edrobotics/rescue_maze_2024/vision/log/sorted/H/4cam2190.png

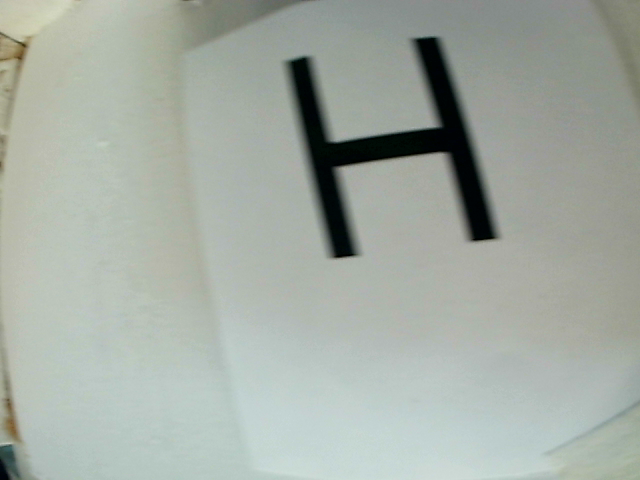
vision/log/sorted/H/4cam2190.png
