edrobotics/rescue_maze_2024/vision/log/sorted/H/5cam2187.png

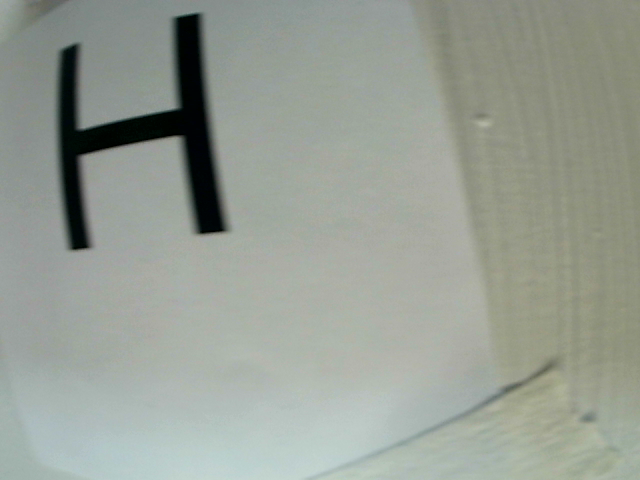
vision/log/sorted/H/5cam2187.png
