edrobotics/rescue_maze_2024/vision/log/sorted/H/6cam2188.png

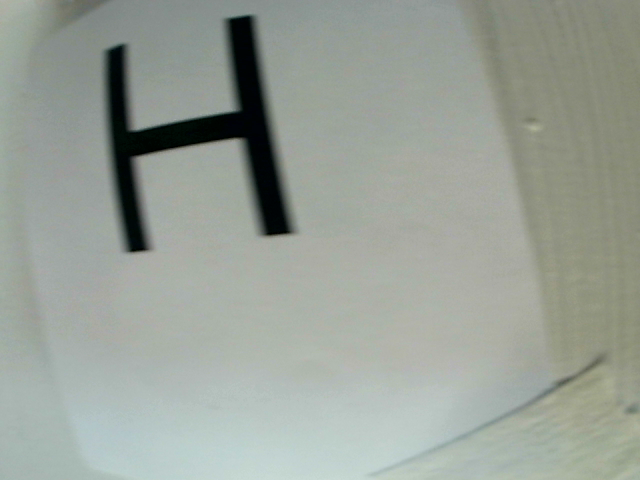
vision/log/sorted/H/6cam2188.png
