edrobotics/rescue_maze_2024/vision/log/sorted/H/7cam2189.png

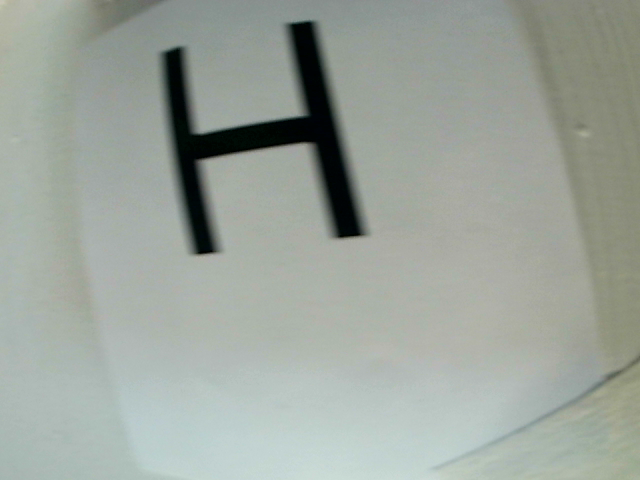
vision/log/sorted/H/7cam2189.png
