edrobotics/rescue_maze_2024/vision/log/sorted/H/8cam2171.png

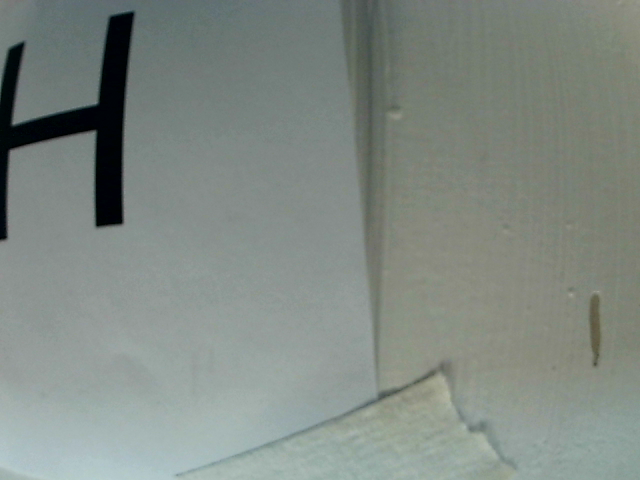
vision/log/sorted/H/8cam2171.png
