edrobotics/rescue_maze_2024/vision/log/sorted/red/17cam2191.png

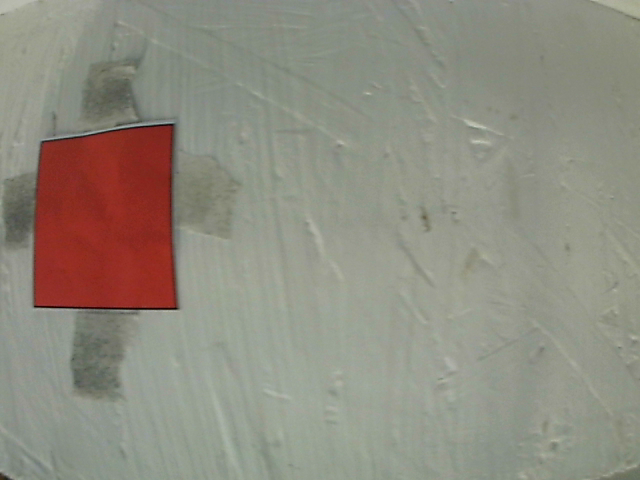
vision/log/sorted/red/17cam2191.png
