edrobotics/rescue_maze_2024/vision/log/sorted/red/18cam2193.png

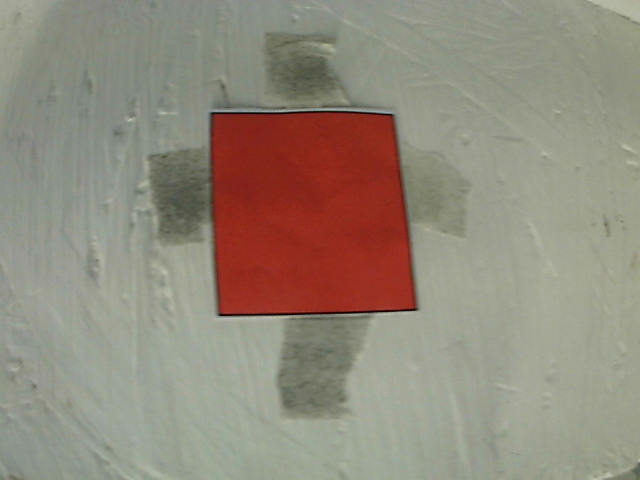
vision/log/sorted/red/18cam2193.png
