edrobotics/rescue_maze_2024/vision/log/sorted/red/19cam2192.png

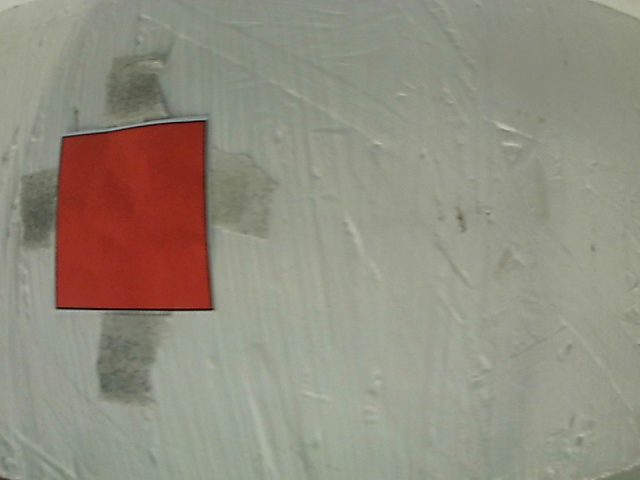
vision/log/sorted/red/19cam2192.png
