edrobotics/rescue_maze_2024/vision/log/sorted/red/20cam2194.png

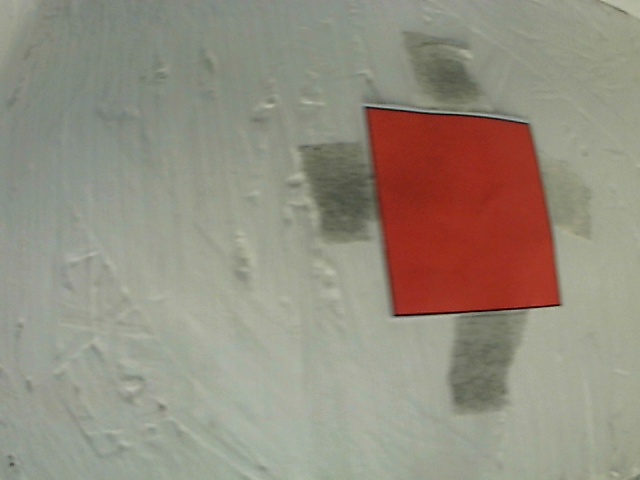
vision/log/sorted/red/20cam2194.png
