edrobotics/rescue_maze_2024/vision/log/sorted/red/21cam1767.png

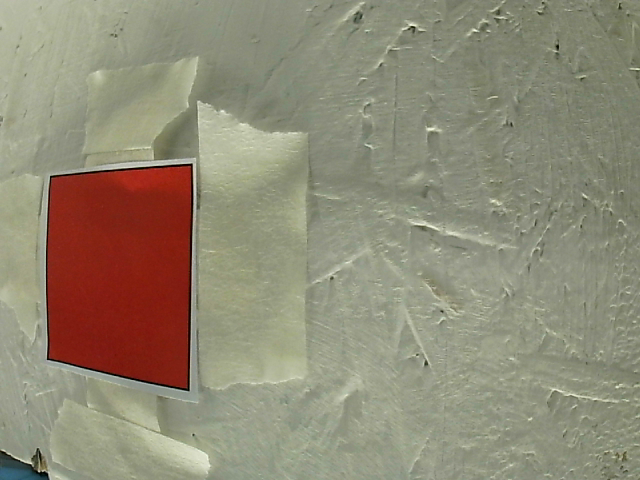
vision/log/sorted/red/21cam1767.png
