edrobotics/rescue_maze_2024/vision/log/sorted/red/24cam1758.png

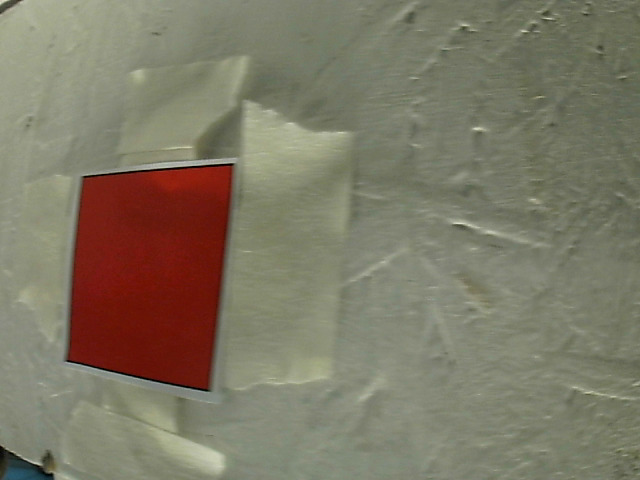
vision/log/sorted/red/24cam1758.png
