edrobotics/rescue_maze_2024/vision/log/sorted/red/31cam1776.png

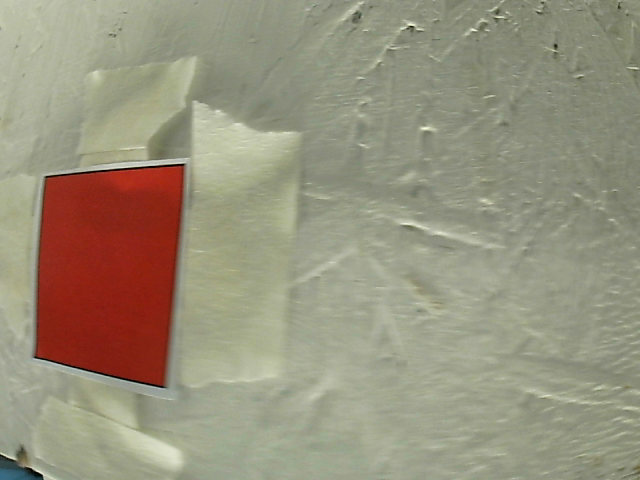
vision/log/sorted/red/31cam1776.png
