edrobotics/rescue_maze_2024/vision/log/sorted/red/34cam1777.png

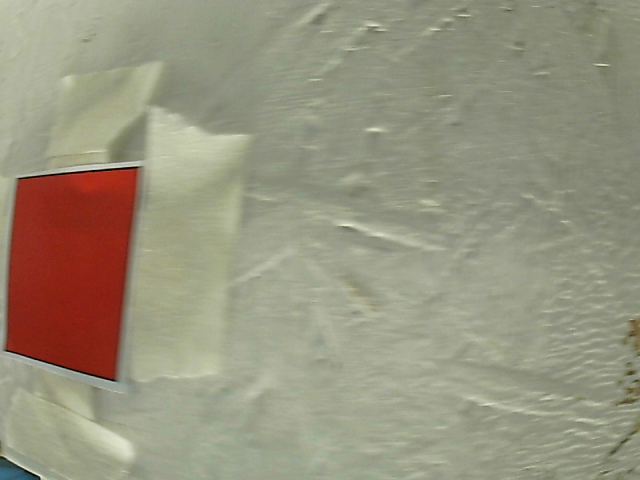
vision/log/sorted/red/34cam1777.png
