edrobotics/rescue_maze_2024/vision/log/sorted/red/cam284.png

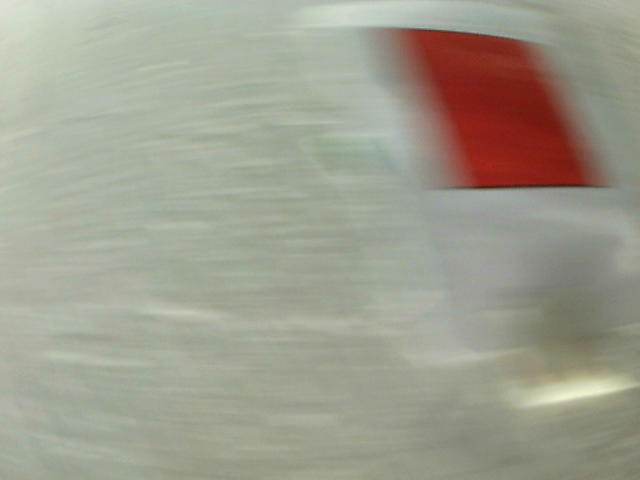
vision/log/sorted/red/cam284.png
