edrobotics/rescue_maze_2024/vision/log/sorted/red/cam1135.png

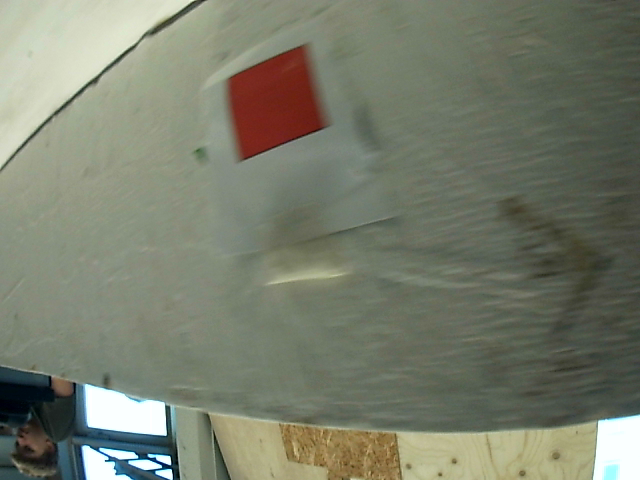
vision/log/sorted/red/cam1135.png
