edrobotics/rescue_maze_2024/vision/log/sorted/red/cam1257.png

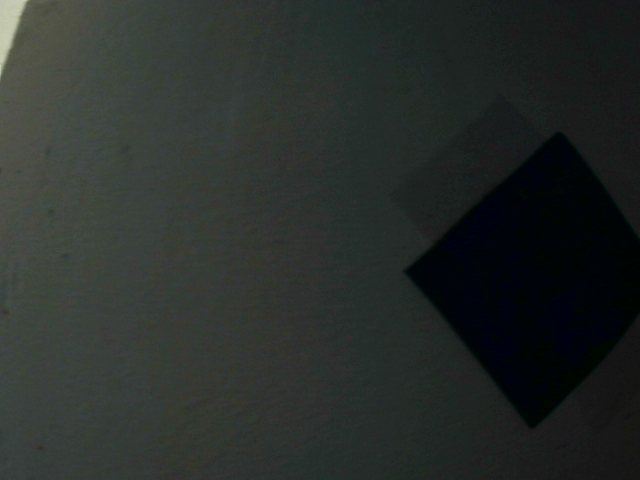
vision/log/sorted/red/cam1257.png
