edrobotics/rescue_maze_2024/vision/log/sorted/red/cam2422.png

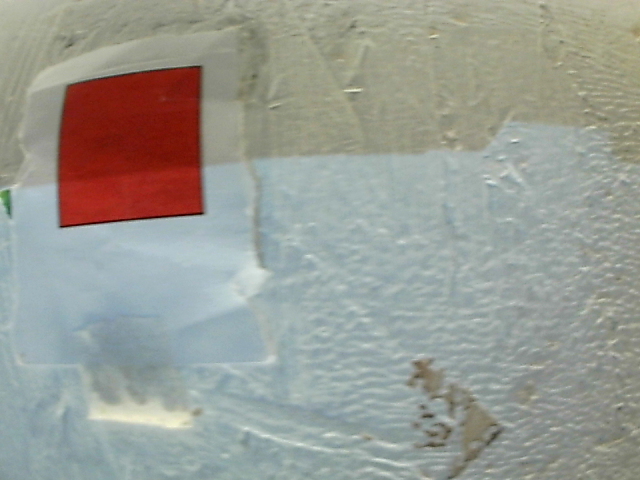
vision/log/sorted/red/cam2422.png
