edrobotics/rescue_maze_2024/vision/log/sorted/red/cam2428.png

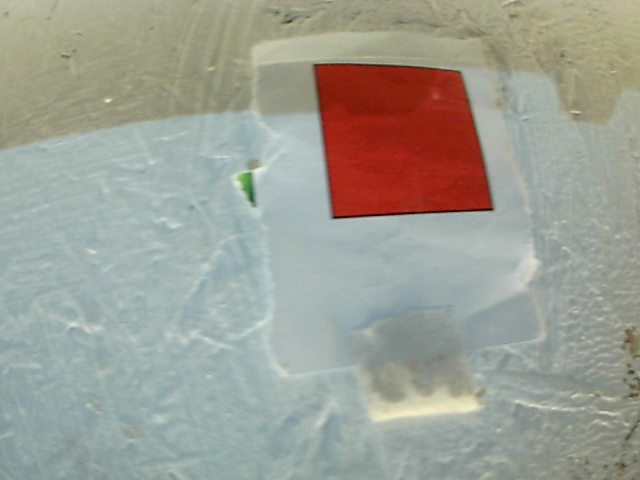
vision/log/sorted/red/cam2428.png
