edrobotics/rescue_maze_2024/vision/log/sorted/red/cam2500.png

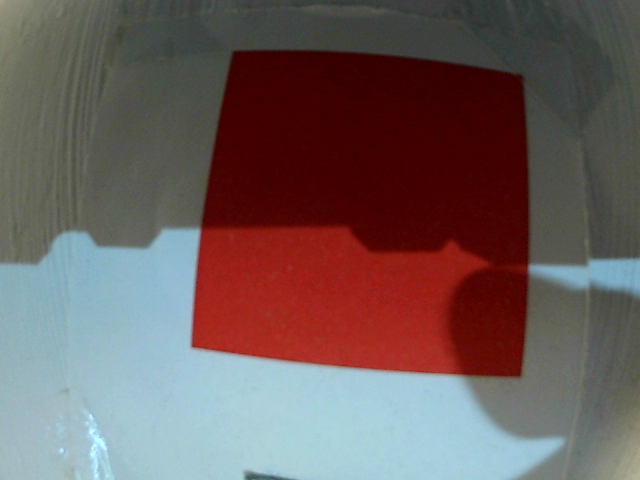
vision/log/sorted/red/cam2500.png
