edrobotics/rescue_maze_2024/vision/log/sorted/yellow/17cam2204.png

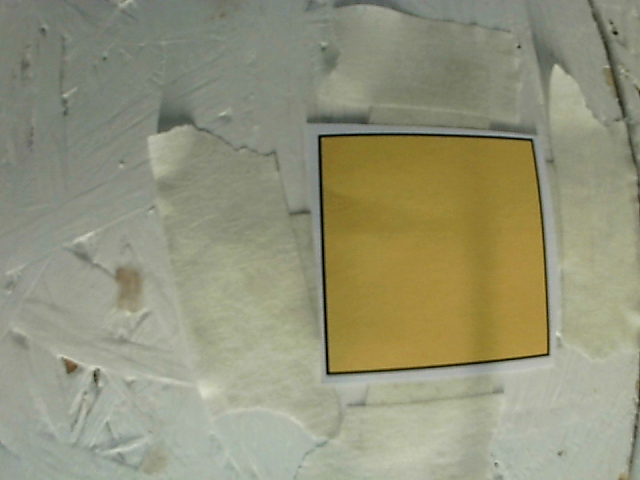
vision/log/sorted/yellow/17cam2204.png
