edrobotics/rescue_maze_2024/vision/log/sorted/yellow/18cam2202.png

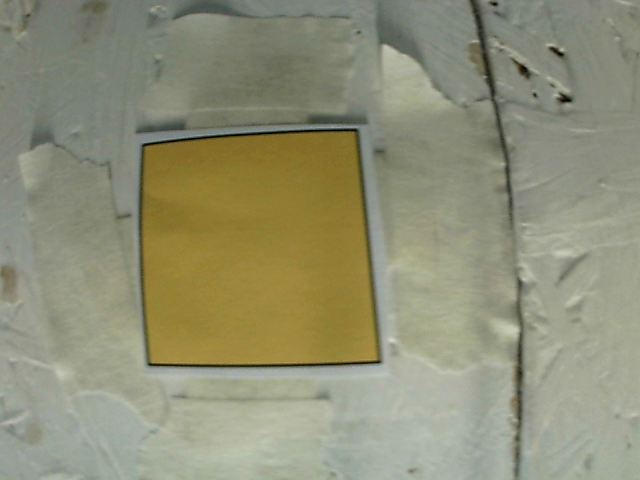
vision/log/sorted/yellow/18cam2202.png
