edrobotics/rescue_maze_2024/vision/log/sorted/yellow/19cam2203.png

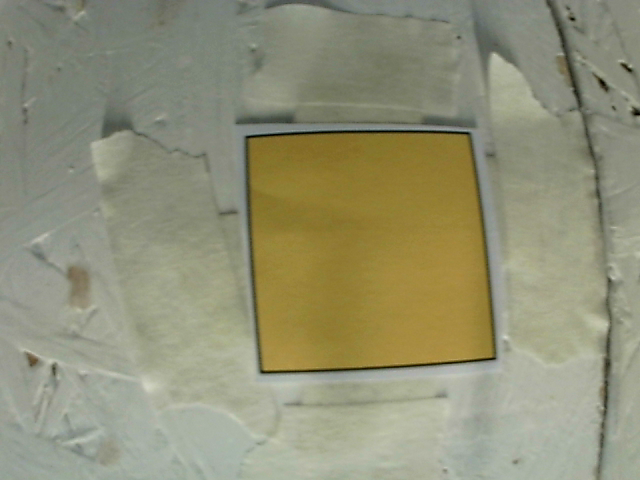
vision/log/sorted/yellow/19cam2203.png
