edrobotics/rescue_maze_2024/vision/log/sorted/yellow/20cam2108.png

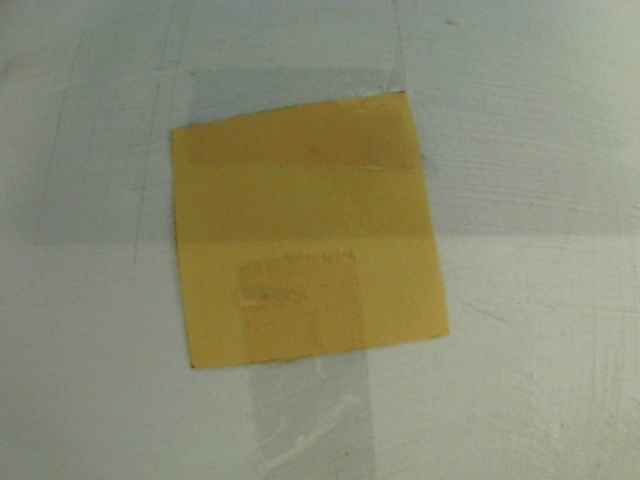
vision/log/sorted/yellow/20cam2108.png
