edrobotics/rescue_maze_2024/vision/log/sorted/yellow/21cam2105.png

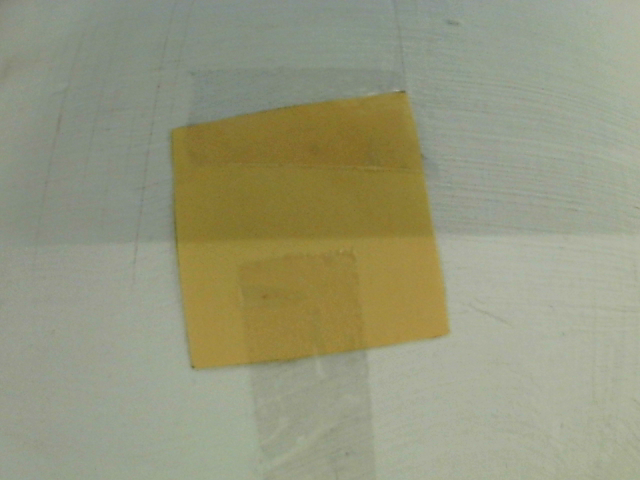
vision/log/sorted/yellow/21cam2105.png
