edrobotics/rescue_maze_2024/vision/log/sorted/yellow/22cam2104.png

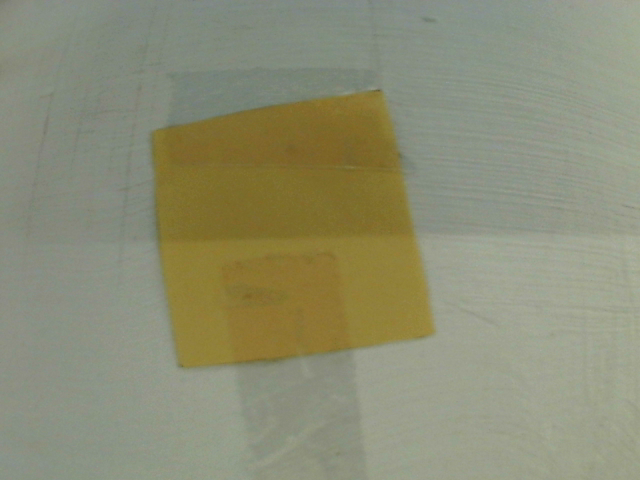
vision/log/sorted/yellow/22cam2104.png
