edrobotics/rescue_maze_2024/vision/log/sorted/yellow/23cam2110.png

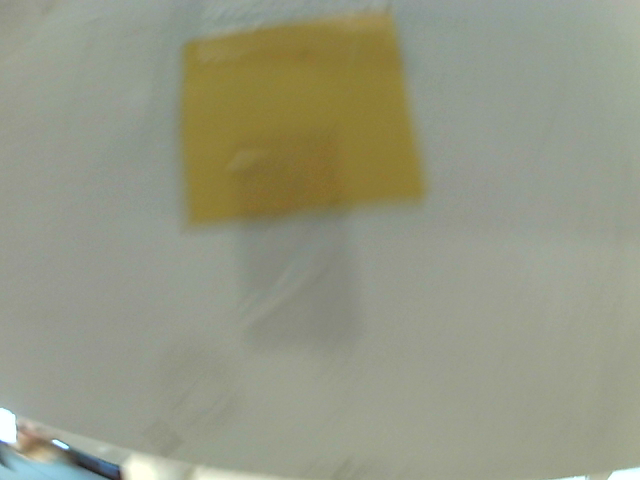
vision/log/sorted/yellow/23cam2110.png
