edrobotics/rescue_maze_2024/vision/log/sorted/yellow/25cam2107.png

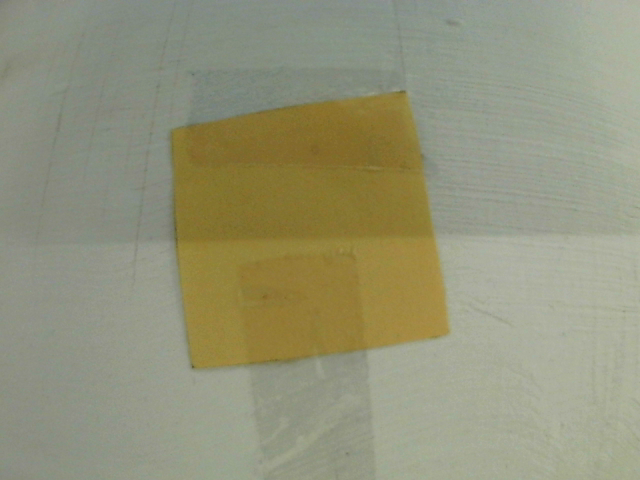
vision/log/sorted/yellow/25cam2107.png
