edrobotics/rescue_maze_2024/vision/log/sorted/yellow/26cam2103.png

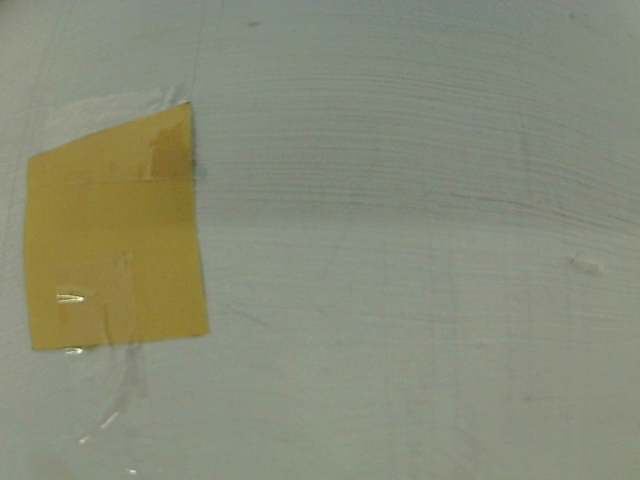
vision/log/sorted/yellow/26cam2103.png
