edrobotics/rescue_maze_2024/vision/log/sorted/yellow/cam290.png

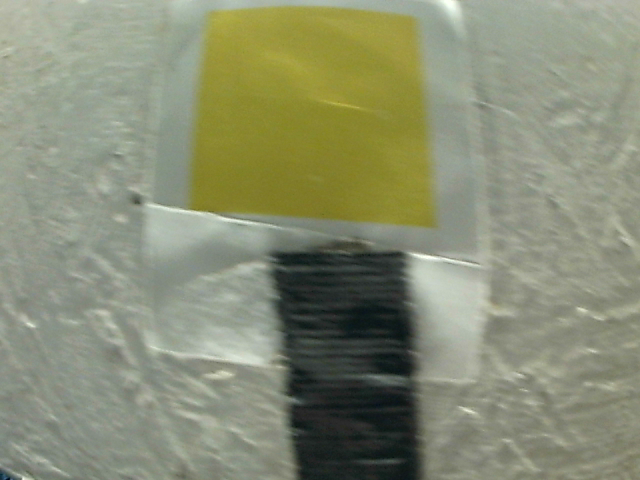
vision/log/sorted/yellow/cam290.png
