edrobotics/rescue_maze_2024/vision/log/sorted/yellow/cam292.png

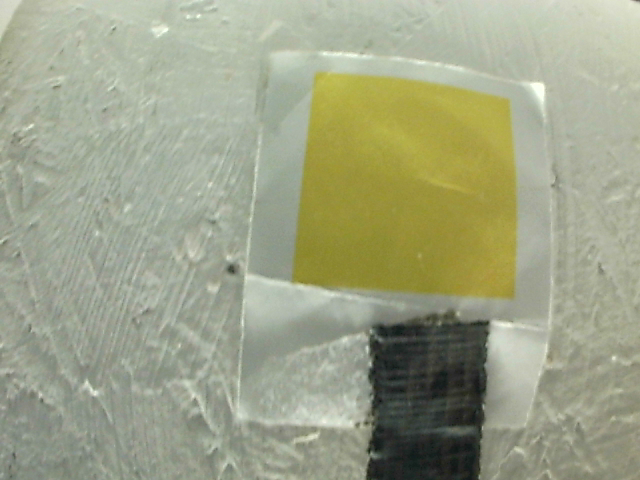
vision/log/sorted/yellow/cam292.png
