edrobotics/rescue_maze_2024/vision/log/sorted/yellow/cam294.png

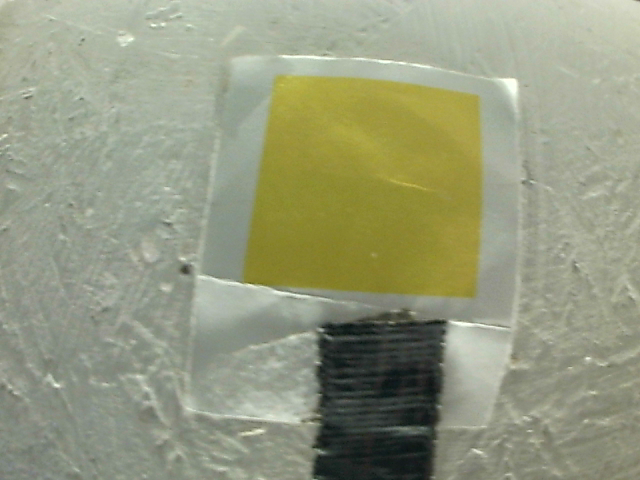
vision/log/sorted/yellow/cam294.png
