edrobotics/rescue_maze_2024/vision/log/sorted/yellow/cam296.png

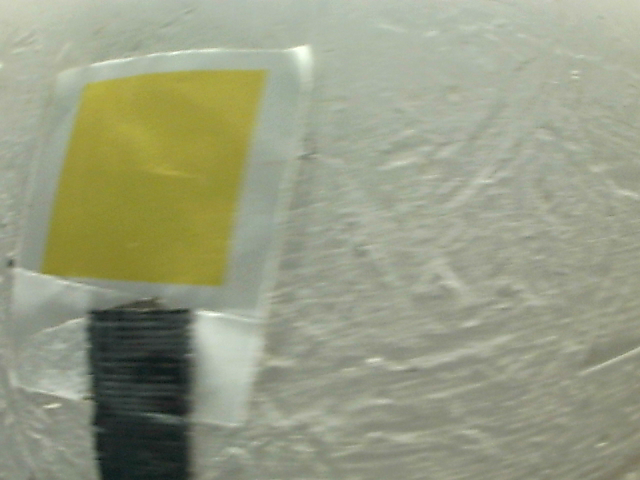
vision/log/sorted/yellow/cam296.png
