edrobotics/rescue_maze_2024/vision/log/sorted/yellow/cam1139.png

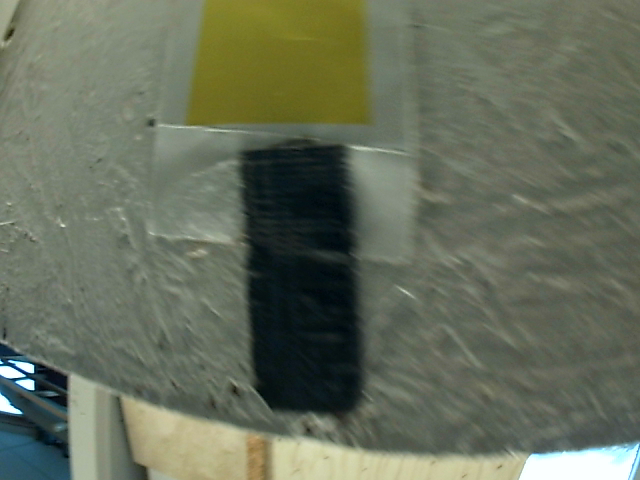
vision/log/sorted/yellow/cam1139.png
