edrobotics/rescue_maze_2024/vision/log/sorted/yellow/cam1141.png

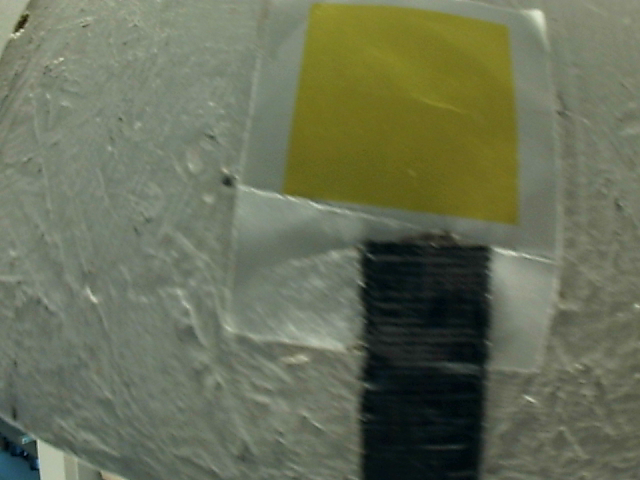
vision/log/sorted/yellow/cam1141.png
