edrobotics/rescue_maze_2024/vision/log/sorted/yellow/cam1145.png

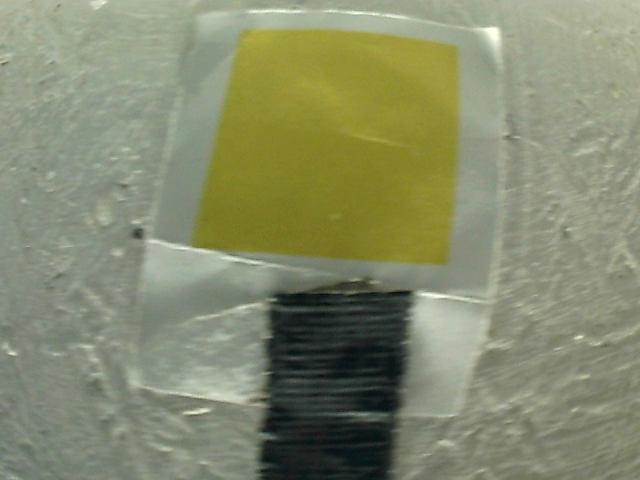
vision/log/sorted/yellow/cam1145.png
