edrobotics/rescue_maze_2024/vision/log/sorted/yellow/cam2214.png

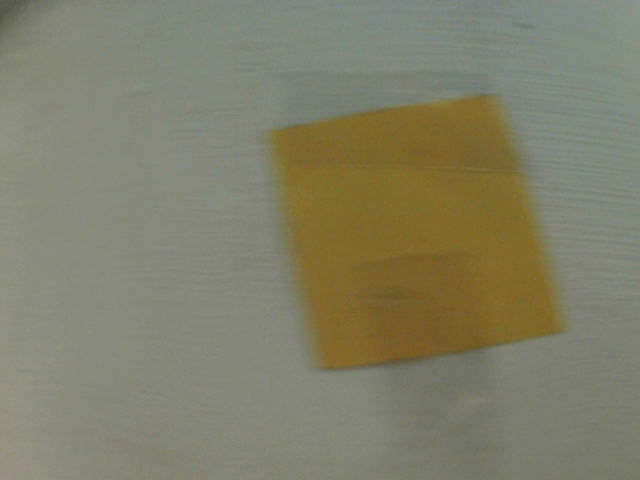
vision/log/sorted/yellow/cam2214.png
