edrobotics/rescue_maze_2024/vision/log/sorted/yellow/cam2442.png

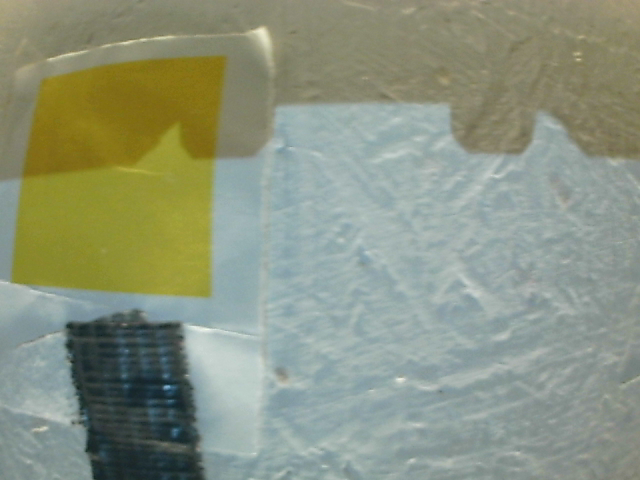
vision/log/sorted/yellow/cam2442.png
