edrobotics/rescue_maze_2024/vision/log/sorted/yellow/cam2446.png

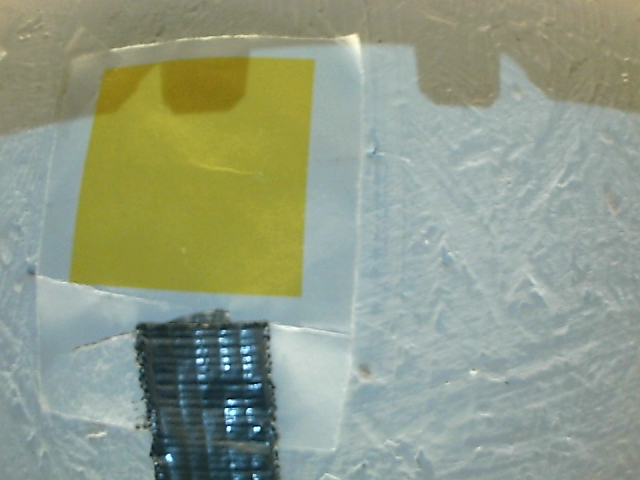
vision/log/sorted/yellow/cam2446.png
