edrobotics/rescue_maze_2024/vision/log/sorted/yellow/cam2448.png

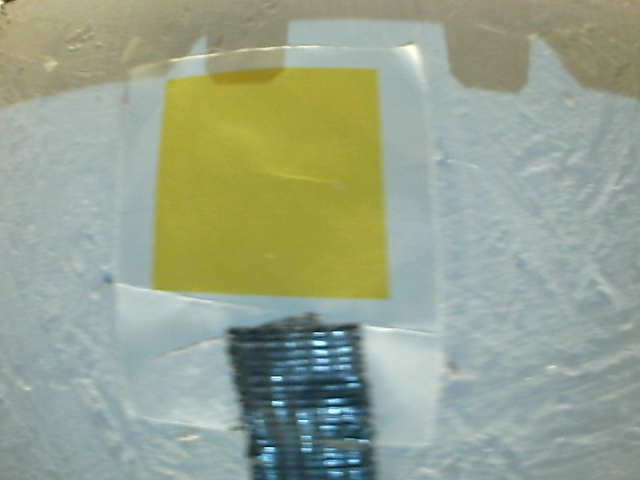
vision/log/sorted/yellow/cam2448.png
