edrobotics/rescue_maze_2024/lowlevel_t41/include/MotorController.h

#ifndef MOTOR_CONTROLLER_H
#define MOTOR_CONTROLLER_H

#include <Arduino.h>
#include <QuickPID.h>
#include <LinearRegression.h>

// Settings for Encoder library
// #define ENCODER_OPTIMIZE_INTERRUPTS // Leads to a linking error
#include <Encoder.h>

class MotorController
{
    public:
    MotorController(int enA, int enB, int pwmPin, int dirPin, double encRatio, int cpr);
    
    bool init();
    // Read encoder positions and set new PID loop value
    bool update();
    // Read encoder positions and calculates values. Does NOT correct, just calculates.
    bool update(bool usePIDCorr);
    // Sets the speed in rpm
    void setSpeed(double speed);
    // Sets the PWM output. Clamps if too great.
    void setPWM(int pwmSpeed);
    // Stop by setting PWM values manually. Ensures no unwanted drift.
    void stopDumb();
    // Stop by using PID algorithm. Should stand still regardless of pushing (probably not needed), but can drift in some cases.
    void stopPID();

    void startDistanceMeasure(); // Begin distance measuring
    // Maybe replace these with passing pointers in the beginning and then updating the values through pointers?
    // Returns the distance turned on output shaft since beginning distance measuring. Measured in mm.
    int16_t getDistanceDiff();
    // Returns the current speed of the output shaft, measured in rpm.
    double getOutputSpeed();
    bool isReversed {false}; // If the direction of the motor is inverted. Should this apply to the encoderPosition as well?

    void printValues();
    void printMotorSpeed();
    void pwmRPMCalibration(); // Calibrate the pwm to rpm curve. Currently outputs csv for calculation in spreadsheet program.


    private:

    // Data about the motor and encoder
    double encOutputRatio; // How many turns the encoder makes for one turn of the output shaft.
    int cpr; // Counts per revolution on the encoder shaft. Only counts rising/falling edges, not both!

    // Encoder tracking
    Encoder encoder;
    long encoderPos {0L}; // Position of the encoder, in ticks. Reversing applies here already. A long should be sufficient for unreasonably large distances...
    float curMotorSpeed {0}; // Current motor speed in rpm
    // double curMotorOutSpeed {0}; // Current output shaft speed in rpm. Not really used?
    // const long MILLIS_PER_MINUTE {long(60000)};
    #define MICROS_PER_MINUTE 60000000L // Bad to use #define? 60e6 micros per minute. Could also use static constexpr

    // Distance measuring
    long tickStartDistance {0L}; // Ticks driven since begin of distancemeasure

    // Motor controlling
    int pwmPin {};
    int dirPin {};
    float motorSpeed {0}; // Wanted motor speed in rpm
    float speedCorrection {}; // Correction output from PID (how to change pwm, not new pwm)
    int curPWM {0}; // Current PWM signal

    // Should have been static, but objects are not independent then?
    unsigned long lastUpdateTime = 0;
    long lastEncoderPos = 0;

    // PID
    float Kp {0.03};
    float Ki {1};
    float Kd {0};
    QuickPID pid {&curMotorSpeed, &speedCorrection, &motorSpeed, Kp, Ki, Kd, QuickPID::pMode::pOnError, QuickPID::dMode::dOnMeas, QuickPID::iAwMode::iAwCondition, QuickPID::Action::direct};
    uint32_t pidSampleTimeUs = 5000; // How often the PID loop should update, in microseconds. Untuned, just a guess

    // Convert an rpm value to the PWM value that should give that speed
    double rpmToPwm(double rpm);
    // Coefficients for linear regression to convert rpm to PWM.
    double regCoeff[2] {0.02678, 0.0}; // Full: 0.0267838563, 
    double& kVal {regCoeff[0]};
    double& mVal {regCoeff[1]};
    // Data points in each direction of 0
    // static constexpr int DATA_POINT_NUM {3};
    // static constexpr int PWM_STEP {60};
    static constexpr int PWM_TEST_NUM {7};
    int PWM_TEST_POINTS[PWM_TEST_NUM] {-220, -150, -100, 0, 220, 150, 100};


    // Hacky workaround for getting distances:
    // Wheel radius in mm
    static constexpr int WHEEL_RADIUS {39};
    static constexpr double WHEEL_CIRCUMFERENCE {2*M_PI*WHEEL_RADIUS};

};


#endif //MOTOR_CONTROLLER_H
