edrobotics/rescue_maze_2024/mazenav/src/localNav/KinematicDriver.cpp

#include "localNav/KinematicDriver.h"

KinematicDriver::KinematicDriver(communication::Communicator* globComm)
{
    this->globComm = globComm;
}

void KinematicDriver::calcSpeeds(double tSpeed, double rSpeed)
{
    // Base driving speed
    double baseSpeed {tSpeed};
    double baseWheelspeedContribution {baseSpeed/WHEEL_RADIUS};

    // Contribution of rotation
    double rotationSpeedAtWheel {WHEEL_TURN_CONTRIBUTION_FACTOR*(rSpeed*WHEEL_TURN_RADIUS)};
    double rotationWheelspeedContribution {rotationSpeedAtWheel/WHEEL_RADIUS};

    // Computation of wheel rotation speeds
    double leftSpeed {baseWheelspeedContribution - rotationWheelspeedContribution};
    double rightSpeed {baseWheelspeedContribution + rotationWheelspeedContribution};

    // Convert from rad/s to rpm
    int leftSpeedrpm = MotorControllers::MotorSpeeds::toRpm(leftSpeed);
    int rightSpeedrpm = MotorControllers::MotorSpeeds::toRpm(rightSpeed);

    // Set the speeds to the motorspeeds variable
    motorSpeeds.lf = leftSpeedrpm;
    motorSpeeds.lb = leftSpeedrpm;
    motorSpeeds.rf = rightSpeedrpm;
    motorSpeeds.rb = rightSpeedrpm;

    // std::cout << "leftSpeed: " << leftSpeed << " , lfSpeedWheel: " << leftSpeedrpm << "\n";

}

void KinematicDriver::setSpeeds()
{
    globComm->motors.setSpeeds(motorSpeeds);
}

void KinematicDriver::stop()
{
    motorSpeeds.lf = 0;
    motorSpeeds.lb = 0;
    motorSpeeds.rf = 0;
    motorSpeeds.rb = 0;
    setSpeeds();
}

void KinematicDriver::testComm()
{
    MotorControllers::MotorSpeeds speeds {};
    motorSpeeds = speeds;
    setSpeeds();
    std::this_thread::sleep_for(std::chrono::milliseconds(600));
    speeds.rf = 100;
    speeds.lf = 100;
    speeds.rb = 100;
    speeds.lb = 100;
    motorSpeeds = speeds;
    setSpeeds();
    std::this_thread::sleep_for(std::chrono::milliseconds(1000));
}
