edrobotics/rescue_maze_2024/mazenav/src/fusion/fusion.cpp

#include <fusion/fusion.h>


i2cCommunicator i2cComm {1};
TeensyCommunicator tComm {0x69, &i2cComm};

MotorControllers motors {&tComm};
Sensors sensors {&tComm, &i2cComm};



VisionCommunicator visionComm;

LackOfProgressChecker lOPChecker;


void fusion::main(communication::Communicator* globComm, PiAbstractor* piAbs)
{
    if(!i2cComm.init())
    {
        std::cout << "Initialization of I2C failed";
    }

    tComm.initiate();

    sensors.init();

    // Set the correct fusion group

    // Create hardware communication thread. Will run indefinetely
    // std::cout << "Spawn hardwarecommunicator... ";
    std::thread hardwareCommunicator(&TeensyCommunicator::runLoopLooper, &tComm);
    // std::cout << "done." << "\n";
    // std::cout << "Spawn motorDriver... ";
    std::thread motorDriver(motorDriveLoopLooper, globComm, &motors);
    // std::cout << "done." << "\n";
    ColourIdentifier colId {};

    ColourCalibrator colCal {};
    colCal.init(piAbs);
    if (colCal.checkActivated())
    {
        colCal.calibrate(&sensors, &colId);
    }

    PoseEstimator poseEstimator {&sensors, &colId};
    poseEstimator.setFusionGroup(PoseEstimator::fg_simple);
    // std::cout << "Spawn poseEstimator... ";
    std::thread poseEst(&PoseEstimator::runLoopLooper, &poseEstimator, globComm);
    // std::cout << "done." << "\n";
    
    std::thread visionServerThread(&VisionCommunicator::visionServerLooper, &visionComm, globComm);

    std::thread lackOfProgressThread(&LackOfProgressChecker::loopChecker, &lOPChecker, globComm, piAbs);
    // while (true)
    // {
    //     colCal.calibrate(&sensors, &colId);
    //     std::cout << "Calibration done\n";
    // }

    poseEst.join();
    // std::cout << "joined\n";
    motorDriver.join();
    hardwareCommunicator.join();
    visionServerThread.join();
    lackOfProgressThread.join();
}

void fusion::motorDriveLoop(communication::Communicator* gCom, MotorControllers* mot)
{
    // Set speeds from gCom to motor control object
    mot->setSpeeds(gCom->motors.getSpeeds());
    // Set values from motor control object to teensy communicator
    mot->setVals();
    // Sleep to not occupy the mutexes
    std::this_thread::sleep_for(std::chrono::milliseconds(1));
}

void fusion::motorDriveLoopLooper(communication::Communicator* gCom, MotorControllers* mot)
{
    while(true)
    {
        motorDriveLoop(gCom, mot);
    }
}
