edrobotics/rescue_maze_2024/shared_lib/TransferData/TransferData.h

// Idea: Either do byte array and copy into it, or make a byte pointer
// Other idea: Use normal datatypes first, but store how many bytes they are allowed to use. Then iterate through them to create the byte array and then iterate backwards to get values again.

#pragma once

#include <stdint.h> // Types
#include <cstring> // memcpy

class TransferData
{
    public:
        // Default constructor
        TransferData();
        // Compose the int into the array
        void compose();
        // Decompose the array into the int
        void decompose();

        void test();
        void composeSettings();

        void decomposeSettings();

        void getByteArr(uint8_t data[]);
        void setByteArr(uint8_t data[]);
        void getControlArr(uint8_t data[]);
        void setControlArr(uint8_t data[]);

        static const int DATA_LEN = 64; // Data length in bytes
        static const int SETTING_LEN = 8;
        uint8_t byteArr[DATA_LEN] {0};
        uint8_t controlArr[SETTING_LEN] {0};

        enum Col
        {
            col_r,
            col_g,
            col_b,
            col_c,
            col_num,
        };

        enum ImuVec
        {
            imu_real,
            imu_i,
            imu_j,
            imu_k,
            imu_num,
        };
        
        // Getters
        bool getTof(uint16_t values[]);
        bool getCol(int index, uint16_t values[]);
        bool getIMU(int index, float values[]);
        bool getRPM(int16_t values[]);
        bool getPos(int16_t values[]);
        bool getRpmControl(int16_t values[]);

        // Setters for teensy-pi
        bool setTof(uint16_t values[]);
        bool setCol(int index, uint16_t values[]);
        bool setIMU(int index, float values[]);
        bool setRPM(int16_t values[]);
        bool setPos(int16_t values[]);
        bool setVoltage(float value);

        // Setters for pi-teensy
        bool setRpmControl(int16_t values[]);


        static const int TOF_NUM = 7;
        static const int COL_NUM = 2;
        static const int IMU_NUM = 1;
        static const int MOTOR_NUM = 4;
    private:
        // Teensy to pi

        uint16_t tofData[TOF_NUM] {0};

        uint16_t colData[COL_NUM][col_num] {0};

        float imuData[IMU_NUM][imu_num] {0};

        int16_t rpmData[MOTOR_NUM] {0};
        int16_t posData[MOTOR_NUM] {0};

        float voltageData {0};

        // Pi to teensy
        int16_t rpmControlVals[MOTOR_NUM] {0};

        // Functions to help serialize
        void u16toB(uint16_t input, uint8_t& byte1, uint8_t& byte2);
        void btoU16(uint8_t input1, uint8_t input2, uint16_t& output);
        
        void s16toB(int16_t input, uint8_t& byte1, uint8_t& byte2);
        void btoS16(uint8_t input1, uint8_t input2, int16_t& output);

        // Convertion between float and int (for IMU data)
        static const int16_t multiplier {32000};
        int16_t floatToInt(float f);
        float intToFloat(int16_t i);
};
