edrobotics/rescue_maze_2024/mazenav/include/GlobalConstants.h

#pragma once

extern const int GRID_SIZE;
extern const int WALL_THICKNESS;

extern const int WHEEL_RADIUS;
extern const int WHEEL_SPACING;
extern const int WHEELBASE;
extern const int WHEEL_TURN_RADIUS;
extern const double WHEEL_TURN_CONTRIBUTION_FACTOR;

extern const double TOF_FY_OFFSET;
extern const double TOF_FX_OFFSET;
extern const double TOF_BY_OFFSET;
extern const double TOF_SX_OFFSET;
extern const double TOF_SY_OFFSET;

extern const double LIDAR_X_OFFSET;
extern const double LIDAR_Y_OFFSET;
