edrobotics/rescue_maze_2024/mazenav/include/fusion/Average.h

#pragma once

#include <vector>
#include <stdexcept>

class ConditionalAverageTerm
{
    public:
    ConditionalAverageTerm(double value, double weight);
    // The value
    double value {};
    // Weight in calculation. 1 is standard. 0 means do not use.
    double weight {1};

    bool operator<(const ConditionalAverageTerm& comp) const;
};


class Average
{
    public:
    std::vector<ConditionalAverageTerm> terms {};
    // Strips away terms with weight=0
    void stripZeroWeight();

    // Calculates the average given the terms
    // If no terms are set to calculate (through their weight or lack of terms), throws runtime_error exception
    double calc(std::vector<ConditionalAverageTerm> terms);
    double calc();

    private:

};
